1LineAtaTime/Pet_Deterrent_ESP32_BLE_AirTag/images/Capture5.PNG

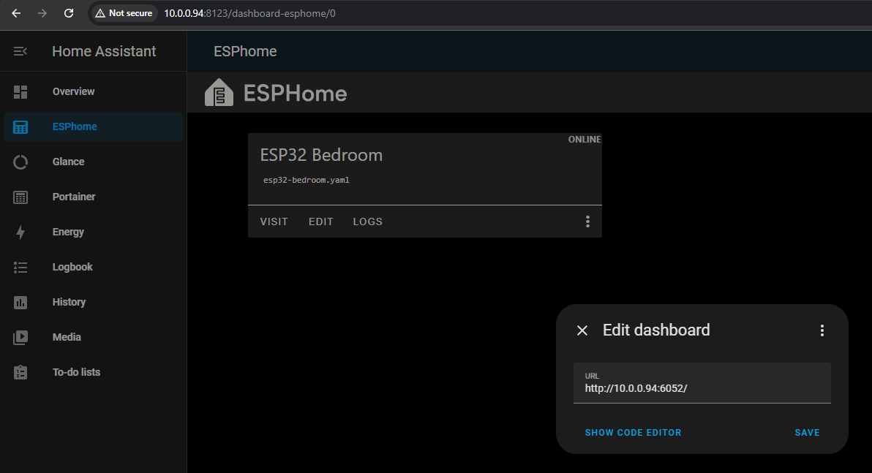
images/Capture5.PNG
