1LineAtaTime/Pet_Deterrent_ESP32_BLE_AirTag/images/Capture7.PNG

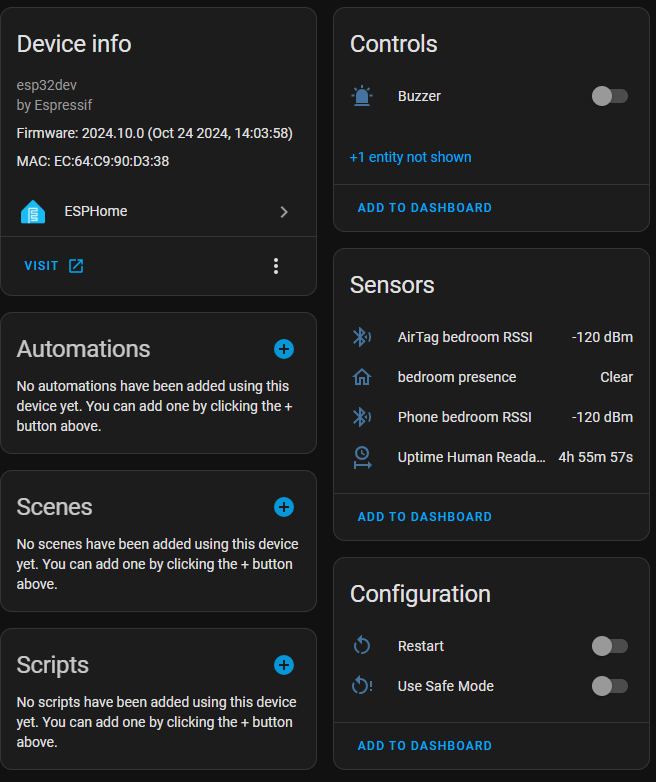
images/Capture7.PNG
