1LineAtaTime/Pet_Deterrent_ESP32_BLE_AirTag/images/Capture9.PNG

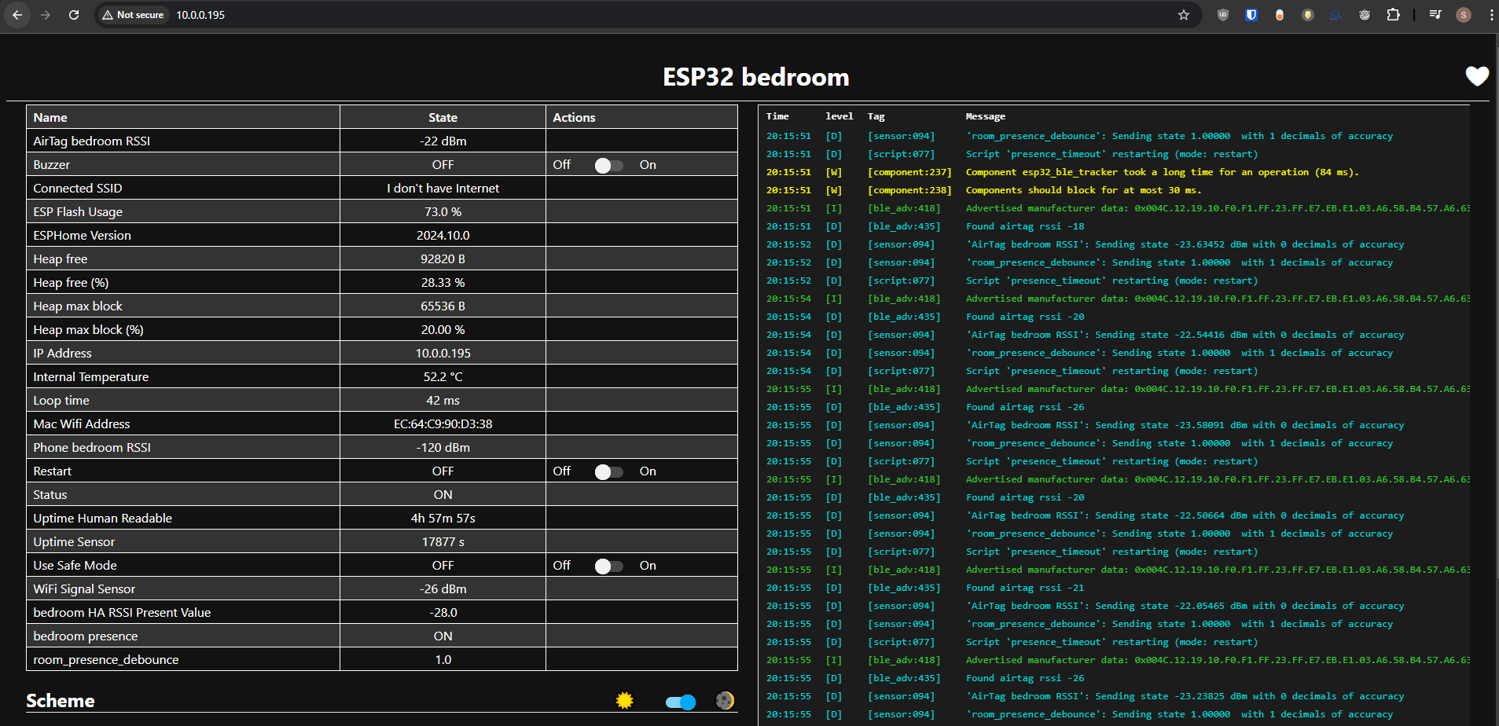
images/Capture9.PNG
