1LineAtaTime/Pet_Deterrent_ESP32_BLE_AirTag/images/Capture23.PNG

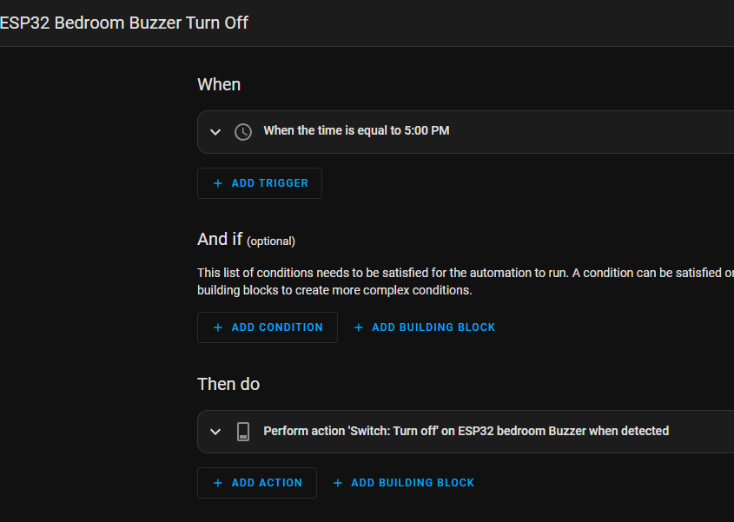
images/Capture23.PNG
